brianpepin/laser/Software/src/views/menu.cpp

#include "globals.h"
#include "fonts.h"
#include "macros.h"
#include "views/menu.h"

template<class T>
static T clamp(T value, T low, T high)
{
    if (value < low) return low;
    if (value > high) return high;
    return value;
}

void MenuView::clearMenu()
{
    for (size_t idx = 0; idx < ARRAYSIZE(_items); idx++)
    {
        auto& item = _items[idx];
        item.text = nullptr;
        memset(item.values, 0, sizeof(Value*) * c_maxItemValues);
    }

    _title = nullptr;
    _sel = 0;
    _valueSelect = 0;
    _fireChannel = Tec::Channel::Vanadate; // disable firing
    _lastFireChannel = _fireChannel;
    _itemCount = 0;
    _buttonIndex = 0xff;

    led.enableFiring(false);
}

void MenuView::addItem(const __FlashStringHelper* text, Cmd cmd, Value* value1, Value* value2, Value* value3)
{
    auto& item = _items[_itemCount];
    item.text = text;
    item.cmd = cmd;
    item.width = 0;
    item.values[0] = value1;
    item.values[1] = value2;
    item.values[2] = value3;

    _itemCount++;
    _update = true;
}

void MenuView::addButton(const __FlashStringHelper* text, Cmd cmd, uint8_t width)
{
    auto& item = _items[_itemCount];
    item.text = text;
    item.cmd = cmd;
    item.width = width;
    memset(item.values, 0, sizeof(Value*) * c_maxItemValues);

    if (_buttonIndex == 0xff)
    {
        _buttonIndex = _itemCount;
    }

    _itemCount++;
    _update = true;
}

void MenuView::mainMenu()
{
    clearMenu();

    size_t idx = 0;
    _values[idx].init(&settings.displayMode);
    addItem(F("DISPLAY MODE"), Cmd::ValueSelect, &_values[idx++]);
    addItem(F("CALIBRATION"), Cmd::Calibration);
    addItem(F("EXIT"), Cmd::Exit);
}

void MenuView::alignmentMenu()
{
    clearMenu();

    // laser firing will be hot here, so reset input state.
    input.reset();
    led.enableFiring(true);
    _fireChannel = Tec::Channel::Pump1;
    _lastFireChannel = _fireChannel;
    
    size_t idx = 0;
    _values[idx].init(ValueType::AlignCurrent, Tec::Channel::Pump1);
    addItem(F("PUMP 1 DRIVE CURRENT"), Cmd::ValueSelect, &_values[idx++]);
    _values[idx].init(ValueType::AlignCurrent, Tec::Channel::Pump2);
    addItem(F("PUMP 2 DRIVE CURRENT"), Cmd::ValueSelect, &_values[idx++]);
    _values[idx].init(&_fireChannel);
    addItem(F("PUMP SELECT"), Cmd::ValueSelect, &_values[idx++]);
    addButton(F("EXIT"), Cmd::CalibrateAlignExit, 6);
}

void MenuView::adcMenu()
{
    clearMenu();

    // laser firing will be hot here, so reset input state.
    input.reset();
    led.enableFiring(true);
    _fireChannel = Tec::Channel::Ktp;
    _lastFireChannel = _fireChannel;

    _setPoints[0] = settings.calibration.power;

    auto* calPoint = &settings.calibration.power;
    auto* setPoint = &_setPoints[0];
    
    _values[0].init(ValueType::Current, calPoint, setPoint);
    _values[1].init(ValueType::Power, calPoint, setPoint);
    _values[2].init(ValueType::Adc, calPoint, setPoint);

    addItem(F("OUTPUT POWER"), Cmd::ValueSelect, &_values[0], &_values[1], &_values[2]);

    addButton(F("SAVE"), Cmd::CalibrateSave, 4);
    addButton(F("CANCEL"), Cmd::CalibrateCancel, 6);
}

void MenuView::calibrationMenu()
{
    clearMenu();
    addButton(F("PUMP 1"), Cmd::CalibratePump1, 10);
    addButton(F("PUMP 2"), Cmd::CalibratePump2, 10);
    addButton(F("VANADATE"), Cmd::CalibrateVanadate, 10);
    addButton(F("KTP"), Cmd::CalibrateKtp, 10);
    addButton(F("ALIGN"), Cmd::CalibrateAlign, 10);
    addButton(F("ADC"), Cmd::CalibrateAdc, 10);
    addButton(F("EXIT"), Cmd::Exit, 10);
}

void MenuView::calibrateItem(const __FlashStringHelper* title, Tec::Channel channel)
{
    clearMenu();

    // laser firing will be hot here, so reset input state.
    input.reset();
    led.enableFiring(true);

    size_t idx = 0;
    _title = title;
    _fireChannel = channel;
    _lastFireChannel = _fireChannel;

    if (channel == Tec::Channel::Pump1 || channel == Tec::Channel::Pump2)
    {
        _values[idx].init(ValueType::MaxCurrent, channel);
        addItem(F("MAX CURRENT"), Cmd::ValueSelect, &_values[idx]);
        idx++;
    }

    if (channel == Tec::Channel::Pump1 || channel == Tec::Channel::Pump2 || channel == Tec::Channel::Ktp)
    {
        _values[idx].init(ValueType::Current, channel);
        addItem(F("DRIVE CURRENT"), Cmd::ValueSelect, &_values[idx]);
        idx++;
    }

    _values[idx].init(ValueType::Temp, channel);
    addItem(F("TEMPERATURE"), Cmd::ValueSelect, &_values[idx]);
    idx++;

    addButton(F("SAVE"), Cmd::CalibrateSave, 4);
    addButton(F("CANCEL"), Cmd::CalibrateCancel, 6);
}

void MenuView::start(View* prevView)
{
    _prevView = prevView;
    laser.enable(false);
    mainMenu();
}

void MenuView::processCmd(Cmd cmd, View** newView)
{
    switch (cmd)
    {
        default:
        case Cmd::Exit:
            settings.save();
            *newView = _prevView;
            break;

        case Cmd::Calibration:
            settings.save();
            calibrationMenu();
            break;

        case Cmd::CalibrateAlign:
            alignmentMenu();
            break;

        case Cmd::CalibrateAdc:
            adcMenu();
            break;

        case Cmd::CalibratePump1:
            calibrateItem(F("PUMP 1"), Tec::Channel::Pump1);
            break;

        case Cmd::CalibratePump2:
            calibrateItem(F("PUMP 2"), Tec::Channel::Pump2);
            break;

        case Cmd::CalibrateVanadate:
            calibrateItem(F("VANADATE"), Tec::Channel::Vanadate);
            break;

        case Cmd::CalibrateKtp:
            calibrateItem(F("KTP"), Tec::Channel::Ktp);
            break;

        case Cmd::CalibrateCancel:
            settings.load();
            Management::restart();
            calibrationMenu();
            break;

        case Cmd::CalibrateAlignExit:
            calibrationMenu();
            break;

        case Cmd::CalibrateSave:
            settings.save();
            Management::restart();
            calibrationMenu();
            break;

        case Cmd::ValueSelect:
            if (_items[_sel].values[0] != nullptr)
            {
                for (uint8_t idx = 0; idx < c_maxItemValues; idx++)
                {
                    if (_items[_sel].values[idx] != nullptr &&
                        !_items[_sel].values[idx]->readOnly())
                    {
                        _valueSelect = idx + 1;
                        _update = true;
                        break;
                    }
                }
            }
            break;
    }
}

bool MenuView::tick(View** newView)
{
    if (_update)
    {
        _update = false;
        return true;
    }

    int8_t dir = input.getEncoderDirection();
    if (dir != 0)
    {
        if (_valueSelect != 0)
        {
            _items[_sel].values[_valueSelect - 1]->adjust(dir, input.getEncoderVelocity());
        }
        else
        {
            _sel += dir;

            if (_sel < 0)
            {
                _sel = 0;
            }
            else if (_sel >= _itemCount)
            {
                _sel = _itemCount - 1;
            }
        }

        return true;
    }

    if (input.getEncoderSelect())
    {
        if (_valueSelect != 0)
        {
            uint8_t newValueSelect = 0;
            for (uint8_t idx = _valueSelect; idx < c_maxItemValues; idx++)
            {
                if (_items[_sel].values[idx] != nullptr &&
                    !_items[_sel].values[idx]->readOnly())
                {
                    newValueSelect = idx + 1;
                    break;
                }
            }

            _valueSelect =  newValueSelect;
            if (_valueSelect == 0)
            {
                laser.enable(false);
            }
        }
        else
        {
            processCmd(_items[_sel].cmd, newView);
        }
        return true;
    }

    if (input.getFireSwitch() != laser.getEnabled() || _fireChannel != _lastFireChannel)
    {
        _lastFireChannel = _fireChannel;
        switch(_fireChannel)
        {
            case Tec::Channel::Pump1:
                laser.enable(input.getFireSwitch(), Laser::Channel::Pump1);
                break;

            case Tec::Channel::Pump2:
                laser.enable(input.getFireSwitch(), Laser::Channel::Pump2);
                break;

            case Tec::Channel::Ktp:
                laser.enable(input.getFireSwitch());
                break;

            default:
                laser.enable(false);
                break;
        }
    }

    bool update = false;

    for (uint8_t item = 0; item < _itemCount; item++)
    {
        for (uint8_t value = 0; value < c_maxItemValues; value++)
        {
            if (_items[item].values[value] != nullptr)
            {
                update |= _items[item].values[value]->tick();
            }
        }
    }

    return update;
}

void MenuView::render()
{
    constexpr static uint8_t margin = 2;

    display.setFontDirection(0);
    u8g2_uint_t y = 0;

    if (_title != nullptr)
    {
        display.setFont(MENU_TITLE);
        y = display.getMaxCharHeight();
        display.setCursor(margin, y);
        display.print(_title);
        y += 2 * margin;
    }

    y += 2;
    display.setFont(MENU_FONT);

    u8g2_uint_t h = display.getMaxCharHeight() + (2 * margin);
    u8g2_uint_t w = display.getDisplayWidth() - 30;
    u8g2_uint_t x = 0;

    // If we have a menu item with more than one value,
    // reserve more space for values.
    u8g2_uint_t divisor = 2;

    for (int8_t item = 0; item < _itemCount; item++)
    {
        if (_items[item].values[1] != nullptr)
        {
            divisor = 3;
            break;
        }
    }

    for (int8_t idx = 0; idx < _itemCount; idx++)
    {
        if (idx == _buttonIndex && idx != 0)
        {
            y += 2 * margin;
            x = w / divisor;
        }

        if (_items[idx].width != 0)
        {
            w = _items[idx].width * display.getMaxCharWidth() + 2 * margin;
        }

        display.setCursor(x + margin, y + h - margin);
        display.print(_items[idx].text);

        display.setCursor(w / divisor + margin, y + h - margin);
        u8g2_uint_t valueWidth = (w - (w / divisor)) / c_maxItemValues;

        for (int valueIdx = 0; valueIdx < c_maxItemValues; valueIdx++)
        {
            Value* value = _items[idx].values[valueIdx];

            if (value == nullptr)
            {
                break;
            }

            u8g2_uint_t valueStartX, valueEndX;
            valueStartX = display.getCursorX();
            value->draw();
            valueEndX = display.getCursorX();

            if (_sel == idx && (valueIdx + 1) == _valueSelect)
            {
                display.drawHLine(valueStartX, y + h - 1, valueEndX - valueStartX);
            }

            //  Add some margin before next value
            display.setCursor(valueStartX + valueWidth, y + h - margin);
        }

        if (_sel == idx && _valueSelect == 0)
        {
            display.drawFrame(x, y, w, h);
        }

        if (idx >= _buttonIndex && (_buttonIndex != 0 || (idx % 2) == 0))
        {
            x += w;
            x += 3 * display.getMaxCharWidth();
        }
        else
        {
            y += h;
            x = 0;
        }
    }
}

void MenuView::Value::init(ValueType type, Tec::Channel channel)
{
    _type = type;
    _channel = channel;
    _fireChannel = nullptr;
    _displayMode = nullptr;
    _value = 0;
}

void MenuView::Value::init(Tec::Channel* fireChannel)
{
    _type = ValueType::Current;
    _channel = Tec::Channel::Pump1;
    _fireChannel = fireChannel;
    _displayMode = nullptr;
    _value = 0;
    updateState();
}

void MenuView::Value::init(DisplayMode* displayMode)
{
    _type = ValueType::Current;
    _channel = Tec::Channel::Pump1;
    _fireChannel = nullptr;
    _displayMode = displayMode;
    _value = 0;
}

void MenuView::Value::init(ValueType type, Settings::Calibration::Point* calibrationPoint, Settings::Calibration::Point* setPoint)
{
    _type = type;
    _channel = Tec::Channel::Ktp;
    _fireChannel = nullptr;
    _displayMode = nullptr;
    _calibrationPoint = calibrationPoint;
    _setPoint = setPoint;
    _value = 0;

    if (_type == ValueType::Current)
    {
        laser.setCurrent(_setPoint->input);
    }
}

void MenuView::Value::draw()
{
    if (_fireChannel)
    {
        const __FlashStringHelper* s;
        switch (*_fireChannel)
        {
            case Tec::Channel::Pump1: s = F("PUMP 1"); break;
            case Tec::Channel::Pump2: s = F("PUMP 2"); break;
            case Tec::Channel::Ktp: s = F("BOTH"); break;
            default: break;
        }
        display.print(s);
    }
    else if (_displayMode)
    {
        const __FlashStringHelper* s;
        switch (*_displayMode)
        {
            case DisplayMode::Current: s = F("DRIVE CURRENT"); break;
            case DisplayMode::Power:   s = F("OUTPUT POWER"); break;
            default: break;
        }
        display.print(s);
    }
    else if (_type == ValueType::Adc)
    {
        display.print("(");
        display.print(_setPoint->adc);
        display.print(")");
    }
    else
    {
        float value = get();
        char* suffix;
        int sig = 1;

        switch (_type)
        {
            case ValueType::Temp:
                suffix = "C";
                break;

            case ValueType::Power:
                suffix = "W";
                sig = 3;
                if (value < 1)
                {
                    value *= 1000;
                    sig = 0;
                    suffix = "mW";
                }
                break;

            default:
                suffix = "A";
        }

        display.print(value, sig);
        display.print(suffix);
    }
}

bool MenuView::Value::tick()
{
    if (_calibrationPoint != nullptr && laser.getEnabled())
    {
        switch (_type)
        {
            case ValueType::Current:
                _setPoint->input = laser.getCurrent();
                return true;

            case ValueType::Adc:
                _setPoint->adc = Management::getSystemStatus().power.adc.laserOutputPower;
                return true;

            case ValueType::Power:
                _setPoint->output = Management::getSystemStatus().power.laserOutputPower;
                return true;
        }
    }

    return false;
}

void MenuView::Value::adjust(int8_t dir, uint8_t velocity)
{
    if (_fireChannel)
    {
        _value += dir;
        if (_value > 2) _value = 2;
        else if (_value < 0) _value = 0;
        updateState();
    }
    else if (_displayMode)
    {
        _value += dir;
        if (_value > 1) _value = 1;
        else if (_value < 0) _value = 0;
        updateState();
    }
    else
    {
        float delta;
        switch (_type)
        {
            case ValueType::Power:
                delta = .001 * dir;
                if (velocity > 5)
                {
                    delta *= (velocity * 10);
                }
                break;

            default:
                delta = .1 * dir * velocity;
                break;
        }

        set(get() + delta);
    }
}

void MenuView::Value::updateState()
{
    if (_fireChannel)
    {
        switch (_value)
        {
            case 0: *_fireChannel = Tec::Channel::Pump1; break;
            case 1: *_fireChannel = Tec::Channel::Pump2; break;
            case 2: *_fireChannel = Tec::Channel::Ktp; break;
        }
    }
    else if (_displayMode)
    {
        *_displayMode = (DisplayMode)(int)_value;
    }
}

float MenuView::Value::get()
{
    switch (_channel)
    {
        case Tec::Channel::Pump1:
            switch (_type)
            {
                case ValueType::MaxCurrent:
                    return settings.limits.maxPump1Current;
                case ValueType::Current:
                case ValueType::AlignCurrent:
                    return laser.getCurrent(Laser::Channel::Pump1);
                case ValueType::Temp:
                    return settings.temps.pump1;
            }
            break;

        case Tec::Channel::Pump2:
            switch (_type)
            {
                case ValueType::MaxCurrent:
                    return settings.limits.maxPump2Current;
                case ValueType::Current:
                case ValueType::AlignCurrent:
                    return laser.getCurrent(Laser::Channel::Pump2);
                case ValueType::Temp:
                    return settings.temps.pump2;
            }
            break;

        case Tec::Channel::Vanadate:
            return settings.temps.vanadate;

        case Tec::Channel::Ktp:
            switch (_type)
            {
                default:
                    break;
                case ValueType::Current:
                    if (_setPoint != nullptr)
                    {
                        return _setPoint->input;
                    }
                    return laser.getCurrent();
                case ValueType::Temp:
                    return settings.temps.ktp;
                case ValueType::Power:
                    return _setPoint->output;
            }
            break;
    }

    return 0;
}

void MenuView::Value::set(float value)
{
    if (_type == ValueType::Temp)
    {
        value = max(value, 0);
        value = min(value, 100);
    }
    else if (_type == ValueType::MaxCurrent)
    {
        value = max(value, 0);
        value = min(value, laser.getDriverMaxCurrent());
    }

    switch (_channel)
    {
        case Tec::Channel::Pump1:
            switch (_type)
            {
                case ValueType::MaxCurrent:
                    settings.limits.maxPump1Current = value;
                    laser.setCurrent(min(
                        laser.getCurrent(Laser::Channel::Pump1),
                        settings.limits.maxPump1Current),
                        Laser::Channel::Pump1);
                    break;
                case ValueType::Current:
                    laser.setCurrent(value, Laser::Channel::Pump1);
                    laser.setCurrent(0, Laser::Channel::Pump2);
                    break;
                case ValueType::AlignCurrent:
                    laser.setCurrent(value, Laser::Channel::Pump1);
                    break;
                case ValueType::Temp:
                    tec.setTemp(_channel, value);
                    settings.temps.pump1 = value;
                    break;
            }
            break;

        case Tec::Channel::Pump2:
            switch (_type)
            {
                case ValueType::MaxCurrent:
                    settings.limits.maxPump2Current = value;
                    laser.setCurrent(min(
                        laser.getCurrent(Laser::Channel::Pump2),
                        settings.limits.maxPump2Current),
                        Laser::Channel::Pump2);
                    break;
                case ValueType::Current:
                    laser.setCurrent(value, Laser::Channel::Pump2);
                    laser.setCurrent(0, Laser::Channel::Pump1);
                    break;
                case ValueType::AlignCurrent:
                    laser.setCurrent(value, Laser::Channel::Pump2);
                    break;
                case ValueType::Temp:
                    tec.setTemp(_channel, value);
                    settings.temps.pump2 = value;
                    break;
            }
            break;

        case Tec::Channel::Vanadate:
            tec.setTemp(_channel, value);
            settings.temps.vanadate = value;
            break;

        case Tec::Channel::Ktp:
            switch (_type)
            {
                default:
                    break;
                case ValueType::Current:
                    laser.setCurrent(value);
                    if (_setPoint != nullptr)
                    {
                        _setPoint->input = laser.getCurrent();

                        if (!laser.getEnabled())
                        {
                            _setPoint->adc = 0;
                        }
                    }
                    break;
                case ValueType::Temp:
                    tec.setTemp(_channel, value);
                    settings.temps.ktp = value;
                    break;
                case ValueType::Power:
                    if (_setPoint->adc != 0)
                    {
                        _setPoint->output = clamp<float>(value, .001, 40.0);
                        *_calibrationPoint = *_setPoint;
                    }
                    break;
            }
            break;
    }
}
