brianpepin/laser/Software/src/settings.cpp

#include <Arduino.h>
#include <EEPROM.h>
#include "settings.h"
#include "config.h"

#define VERSION 2

static uint16_t _DefaultAdcFromPower(float power)
{
    // (y - b) / m = x;
    return (power - Calibration::LaserMonitor::Offset) / Calibration::LaserMonitor::Slope;
}

void Settings::load()
{
    uint8_t ver = EEPROM.read(0);

    if (ver == VERSION)
    {
        EEPROM.get(1, *this);
    }
    else
    {
        limits.maxPump1Current = ::Limits::Current::Pump1;
        limits.maxPump2Current = ::Limits::Current::Pump2;

        temps.pump1 = ::Defaults::Temperatures::Pump1;
        temps.pump2 = ::Defaults::Temperatures::Pump2;
        temps.vanadate = ::Defaults::Temperatures::Vanadate;
        temps.ktp = ::Defaults::Temperatures::Ktp;

        calibration.power.input = 50.0;
        calibration.power.output = 1.3;
        calibration.power.adc = _DefaultAdcFromPower(calibration.power.output);

        current = 0;
        displayMode = DisplayMode::Current;
    }
}

void Settings::save()
{
    EEPROM.update(0, VERSION);
    EEPROM.put(1, *this);
}
